Chethan222/Tool-tip-temperature-measurement-using-Arduino-and-Python/images/MAX6675-K-Type-Thermocouple-Circuit.jpg

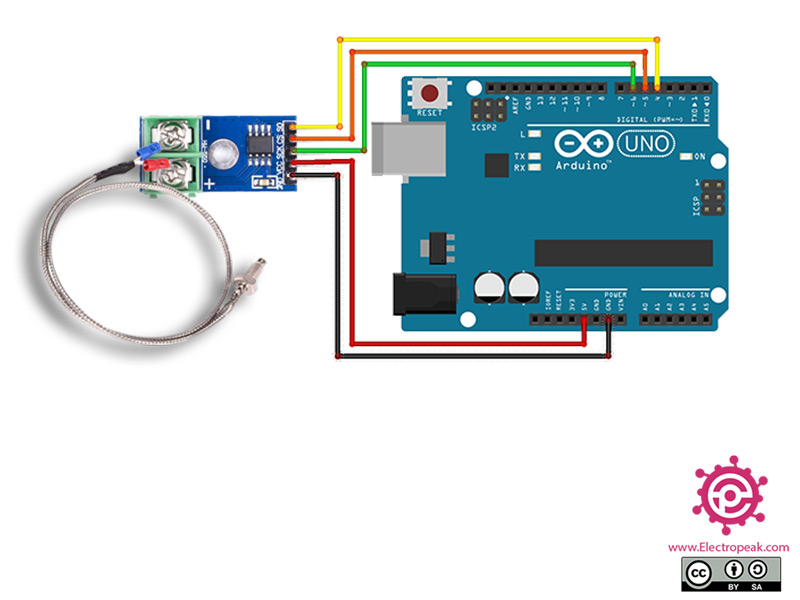
images/MAX6675-K-Type-Thermocouple-Circuit.jpg
