Chethan222/Tool-tip-temperature-measurement-using-Arduino-and-Python/images/Untitled.png

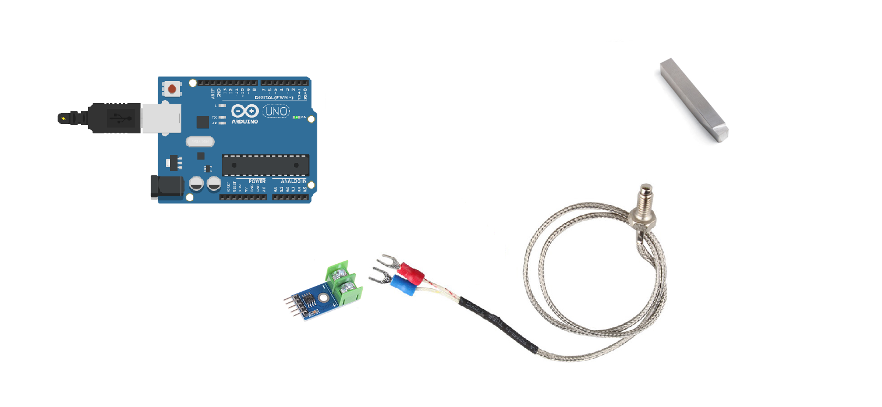
images/Untitled.png
